0xjmux/ESP-PROG-Adapter/files/esp-prog-adapter-v1.0-PCB_F.png

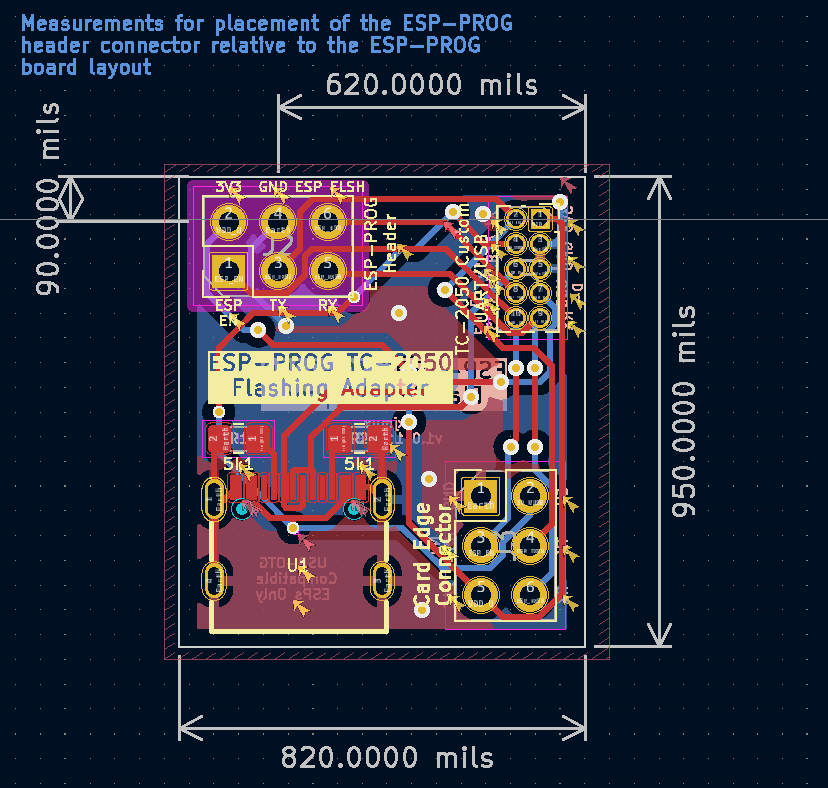
files/esp-prog-adapter-v1.0-PCB_F.png
