0xjmux/ESP-PROG-Adapter/files/esp-prog-adapter-v1.0-render_B_RayT.png

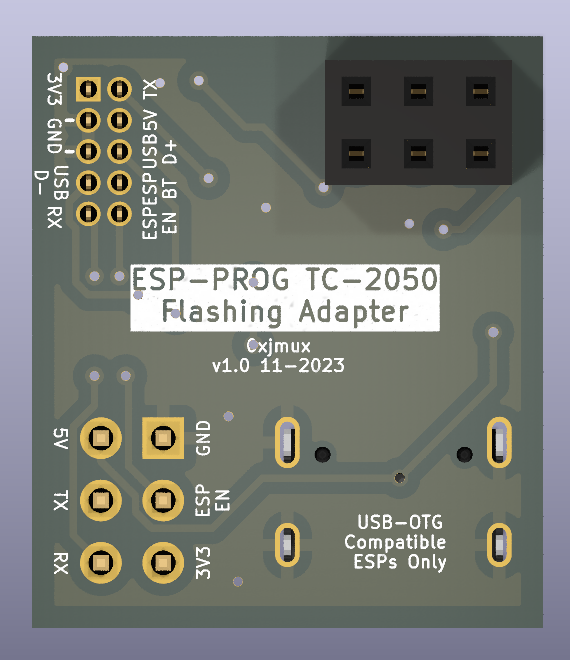
files/esp-prog-adapter-v1.0-render_B_RayT.png
