0xjmux/ESP-PROG-Adapter/files/ESP-PROG-Adapter-v1.1-PCB_F.png

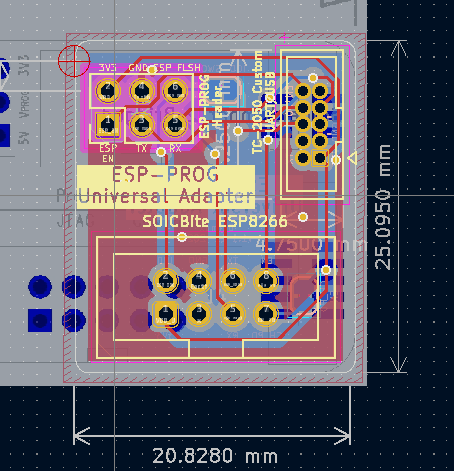
files/ESP-PROG-Adapter-v1.1-PCB_F.png
