0xjmux/ESP-PROG-Adapter/files/ProgConn-SOICBite-Symbol-Example.png

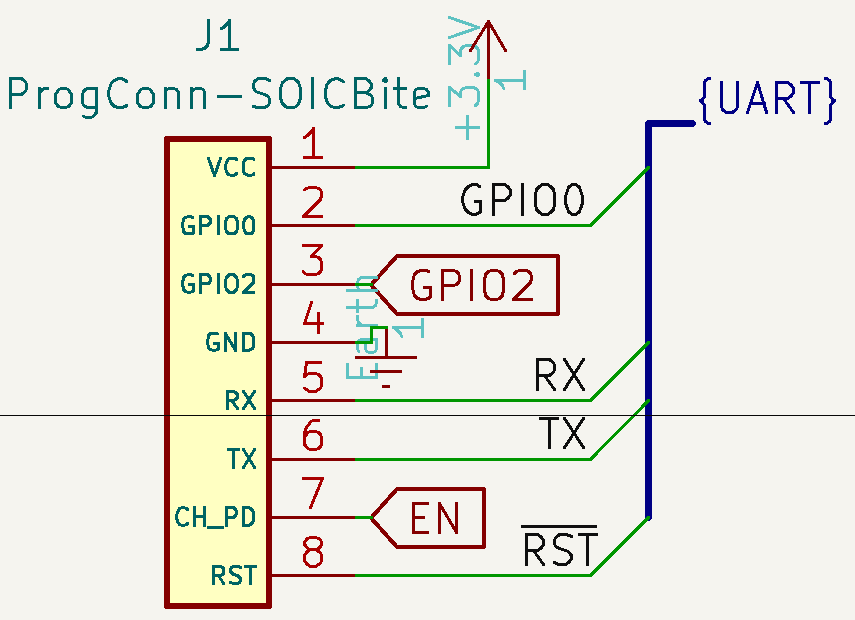
files/ProgConn-SOICBite-Symbol-Example.png
